How2-Oh/Ped101/Pix/Miles_Display.jpg

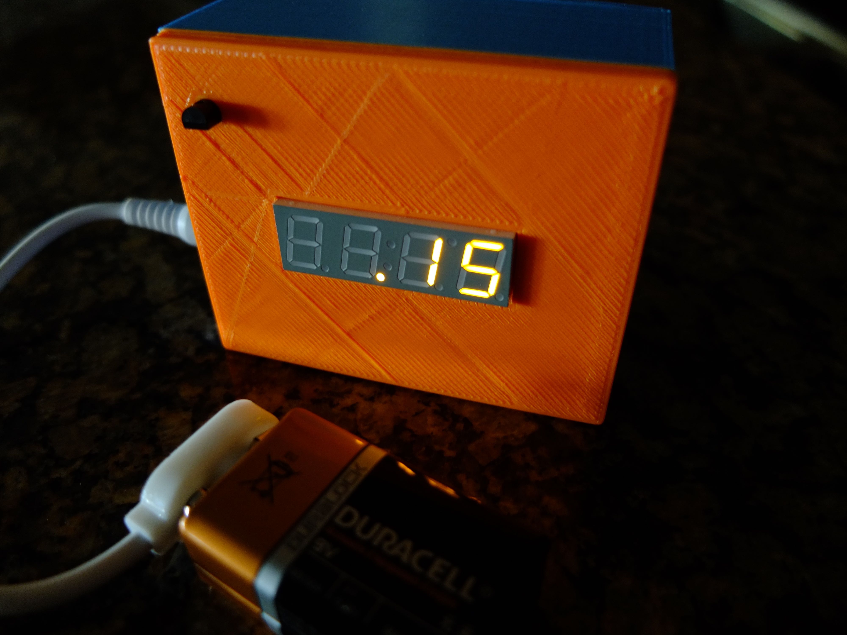
Pix/Miles_Display.jpg
