How2-Oh/Ped101/Pix/Straps_Washers.jpg

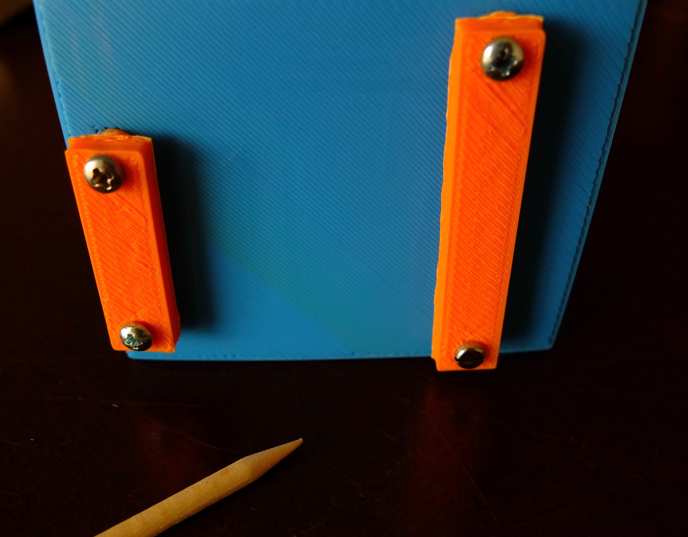
Pix/Straps_Washers.jpg
