How2-Oh/Ped101/Pix/Temp_Display.jpg

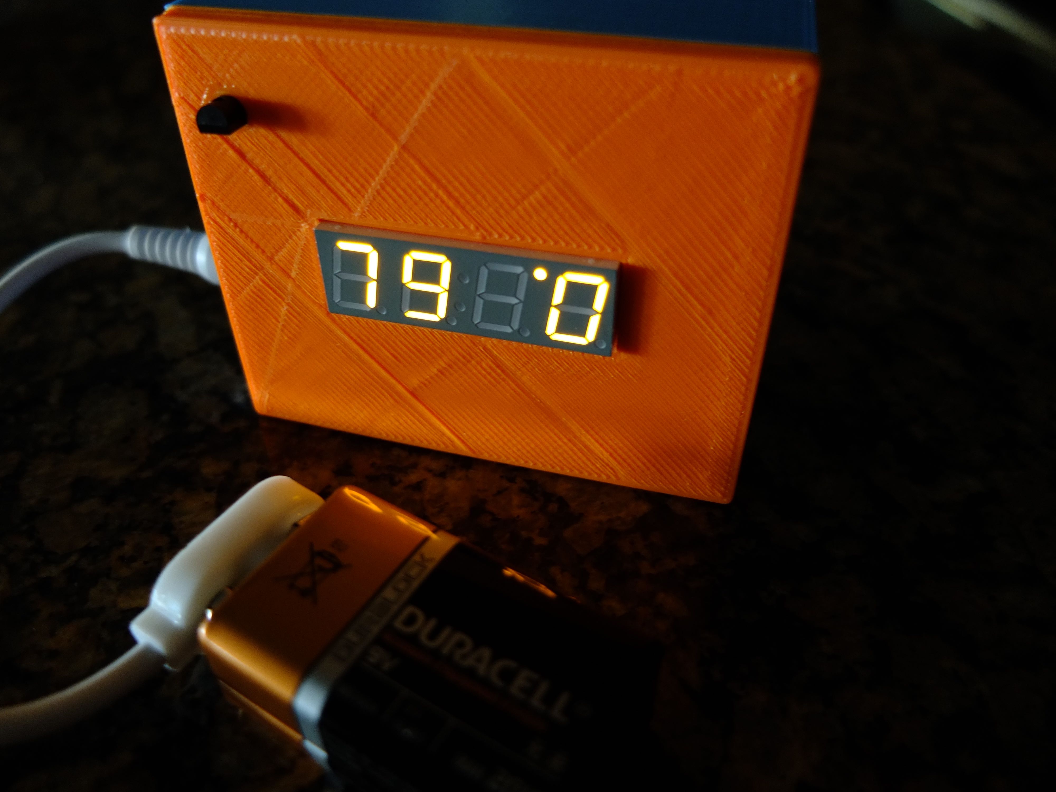
Pix/Temp_Display.jpg
