How2-Oh/Ped101/Pix/Steps_DIsplay.jpg

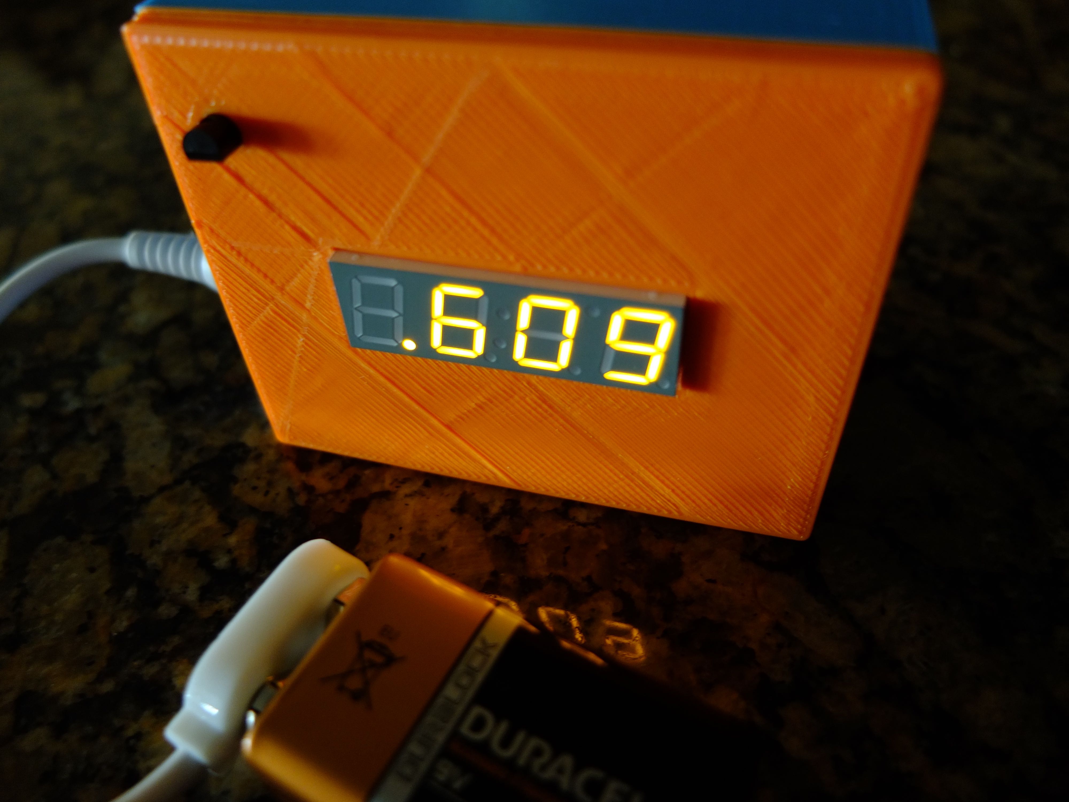
Pix/Steps_DIsplay.jpg
